antoine3000/iot-meditation-link/arduino-code/iot_meditation_device_02/env_example.h

const char* env_ssid = "wifi_network";
const char* env_password = "wifi_password";
const char* env_mqtt_server = "mqtt_server.com";
const char* env_mqtt_topic_1 = "s8xg9cjw2adlb1qm";
const char* env_mqtt_topic_2 = "ukah1rhx7q0j1mth";
